waagsociety/air_quality_sensor_kit/Bora_Lora_Kit/eagle_files/lora_shield_top.png

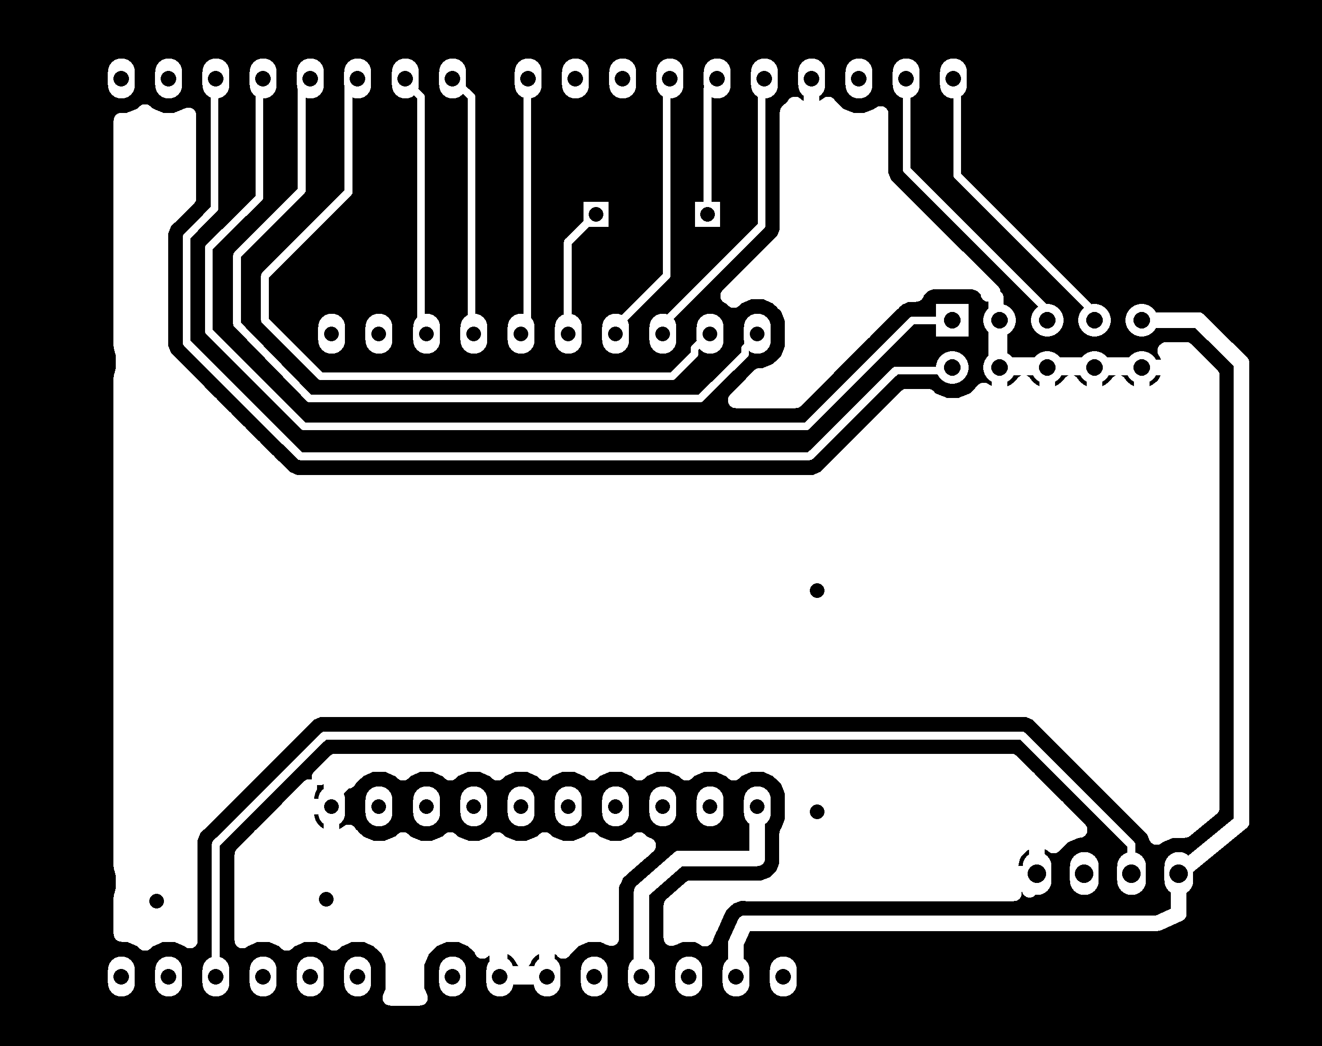
Bora_Lora_Kit/eagle_files/lora_shield_top.png
