waagsociety/air_quality_sensor_kit/MUV Kit/Case/Images/Process Photos/Process8.jpg

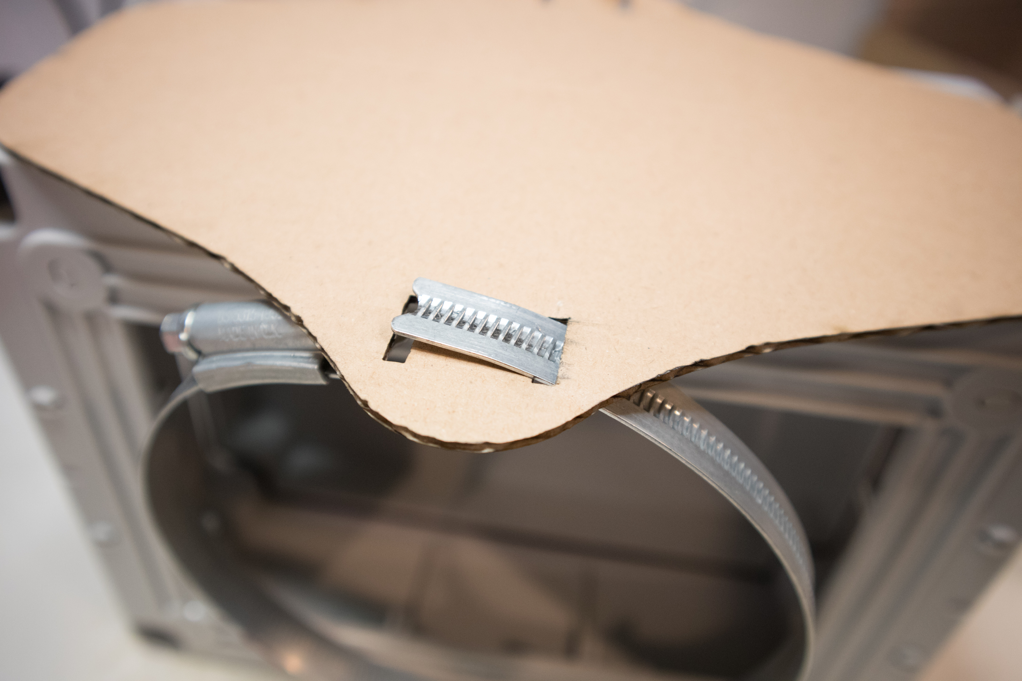
MUV Kit/Case/Images/Process Photos/Process8.jpg
