waagsociety/air_quality_sensor_kit/MUV Kit/Case/Images/Process Photos/Process21.jpg

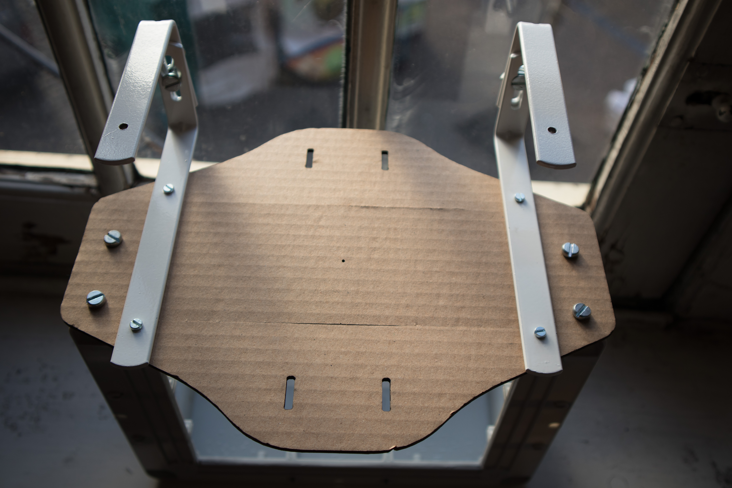
MUV Kit/Case/Images/Process Photos/Process21.jpg
