waagsociety/air_quality_sensor_kit/MUV Kit/Case/Images/Product Photos/Product2.jpg

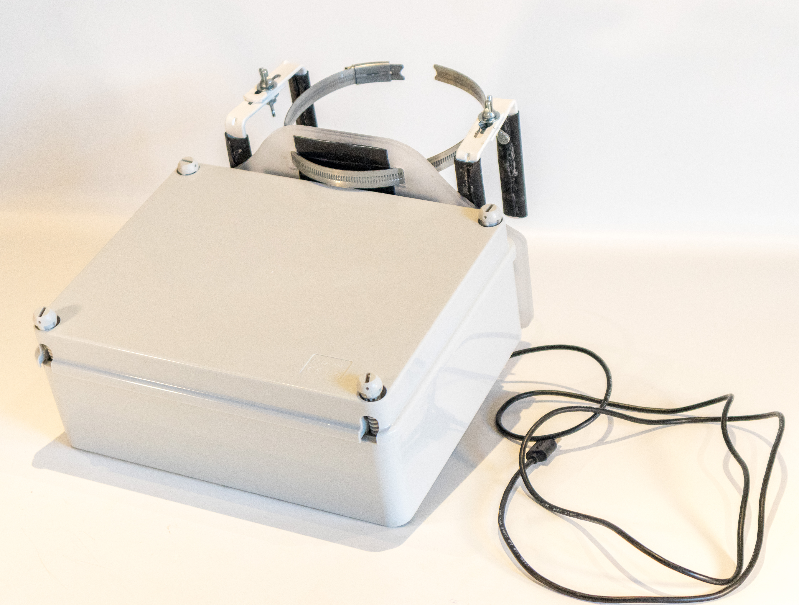
MUV Kit/Case/Images/Product Photos/Product2.jpg
