waagsociety/air_quality_sensor_kit/MUV Kit/Case/Images/Product Photos/Product4.jpg

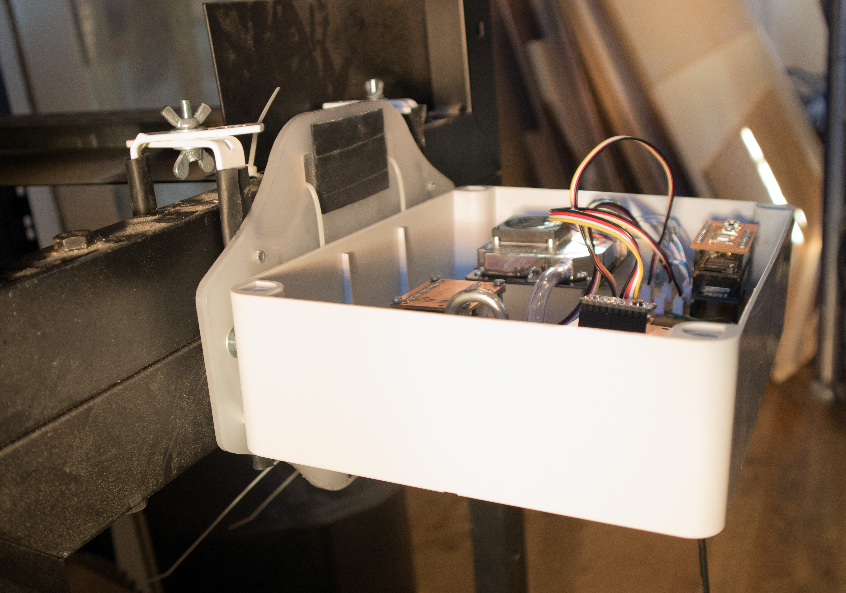
MUV Kit/Case/Images/Product Photos/Product4.jpg
