waagsociety/air_quality_sensor_kit/MUV Kit/Hardware/Machinable files/bme280_pcb_top_cut.png

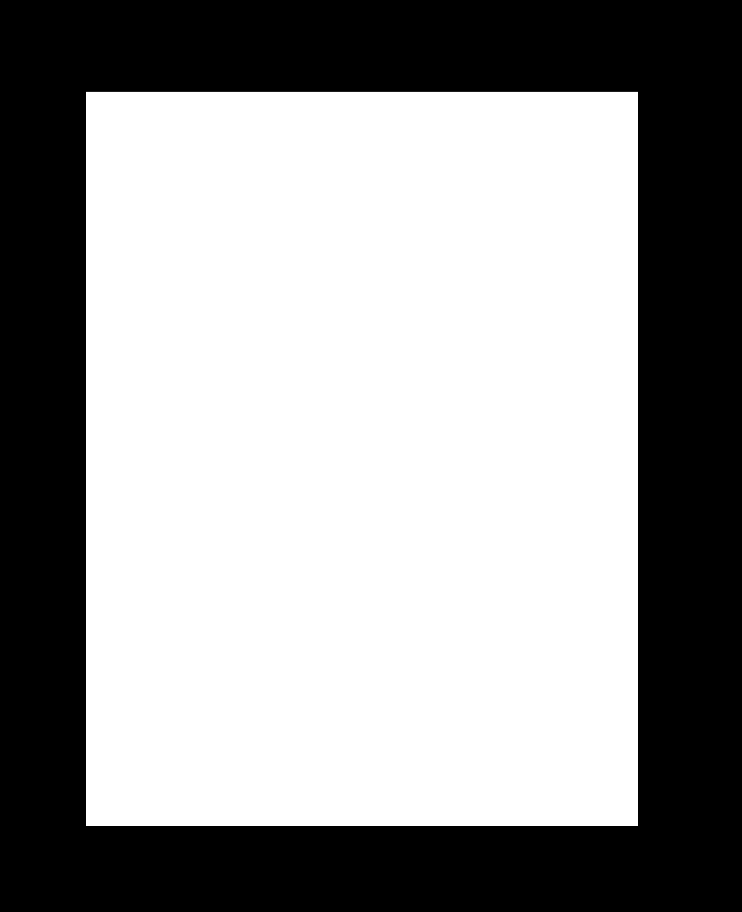
MUV Kit/Hardware/Machinable files/bme280_pcb_top_cut.png
