waagsociety/air_quality_sensor_kit/MUV Kit/Hardware/Machinable files/gas_pcb_bottom_cut.png

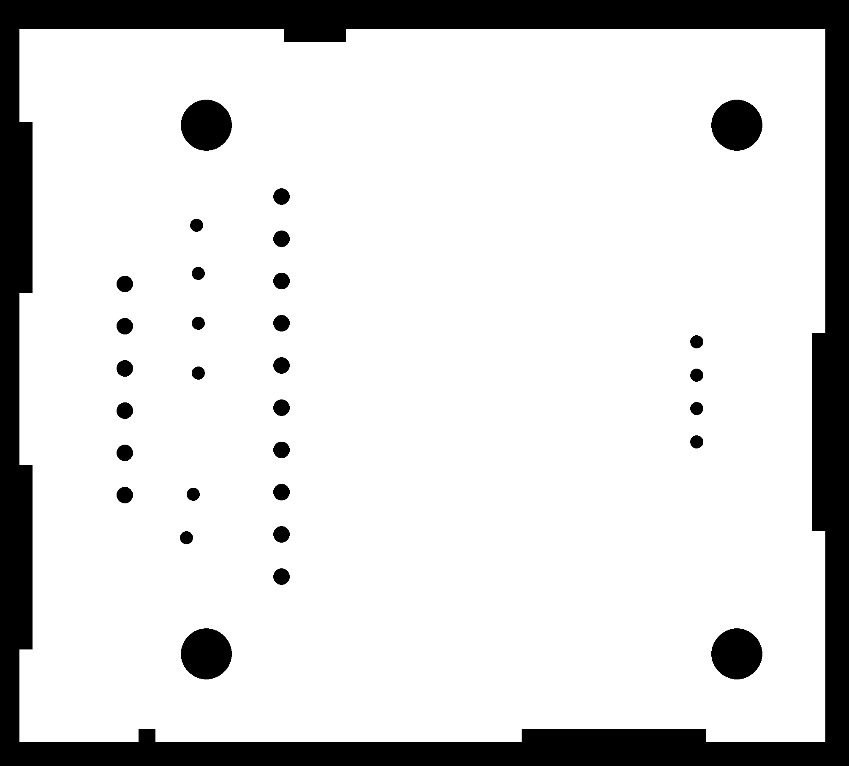
MUV Kit/Hardware/Machinable files/gas_pcb_bottom_cut.png
