waagsociety/air_quality_sensor_kit/MUV Kit/Hardware/Machinable files/interface_pcb_cut.png

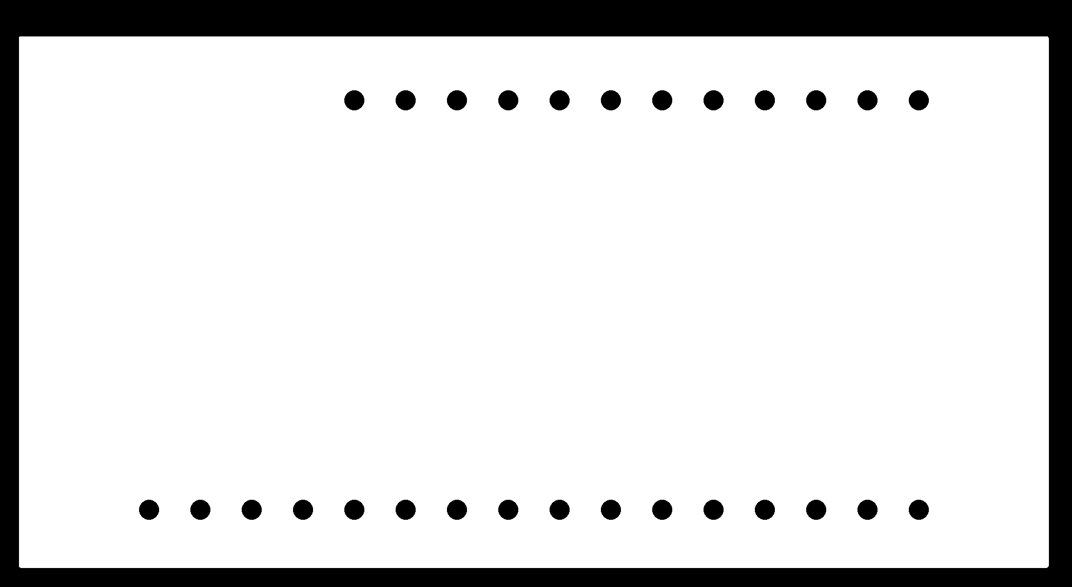
MUV Kit/Hardware/Machinable files/interface_pcb_cut.png
