waagsociety/air_quality_sensor_kit/MUV Kit/Hardware/Machinable files/interface_pcb_traces.png

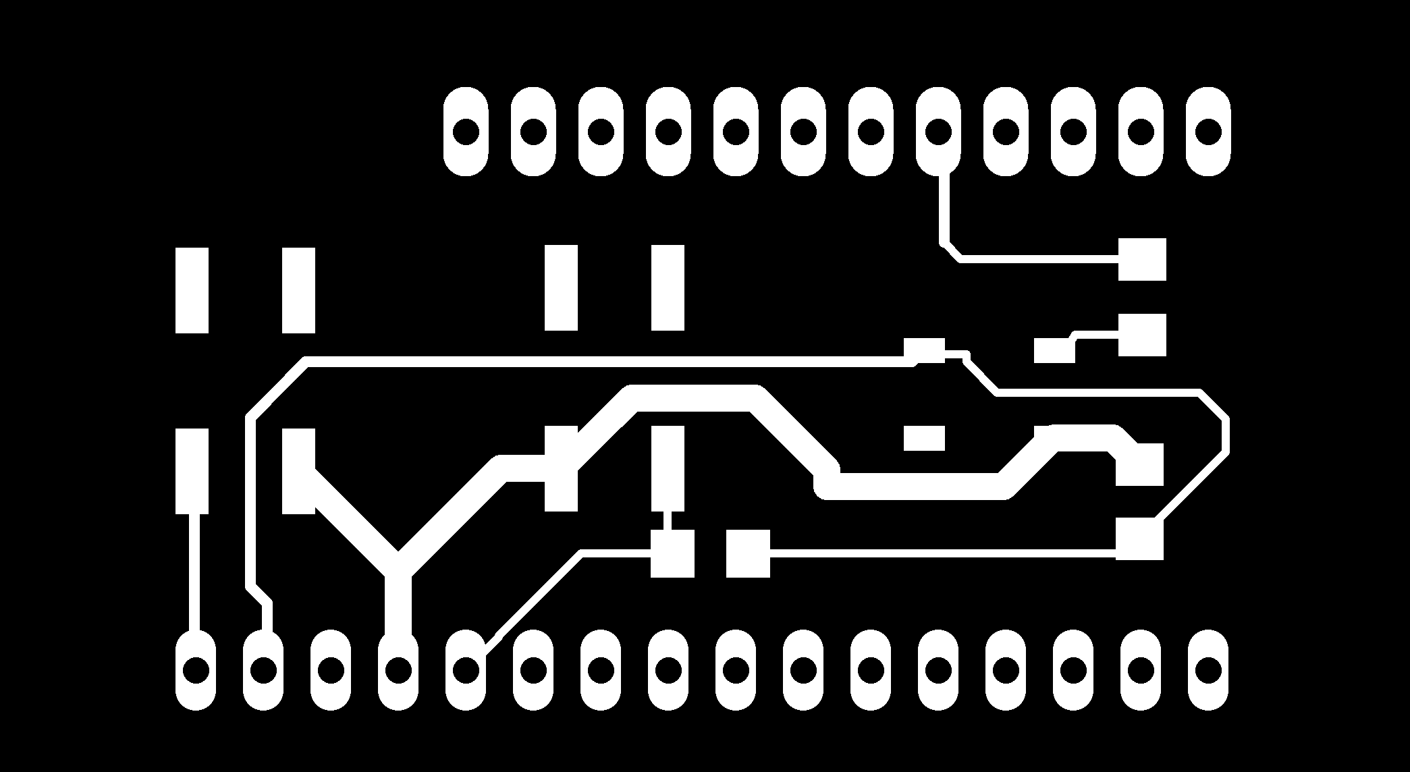
MUV Kit/Hardware/Machinable files/interface_pcb_traces.png
