waagsociety/air_quality_sensor_kit/MUV Kit/Hardware/Machinable files/muv_sensors_pcb_traces.png

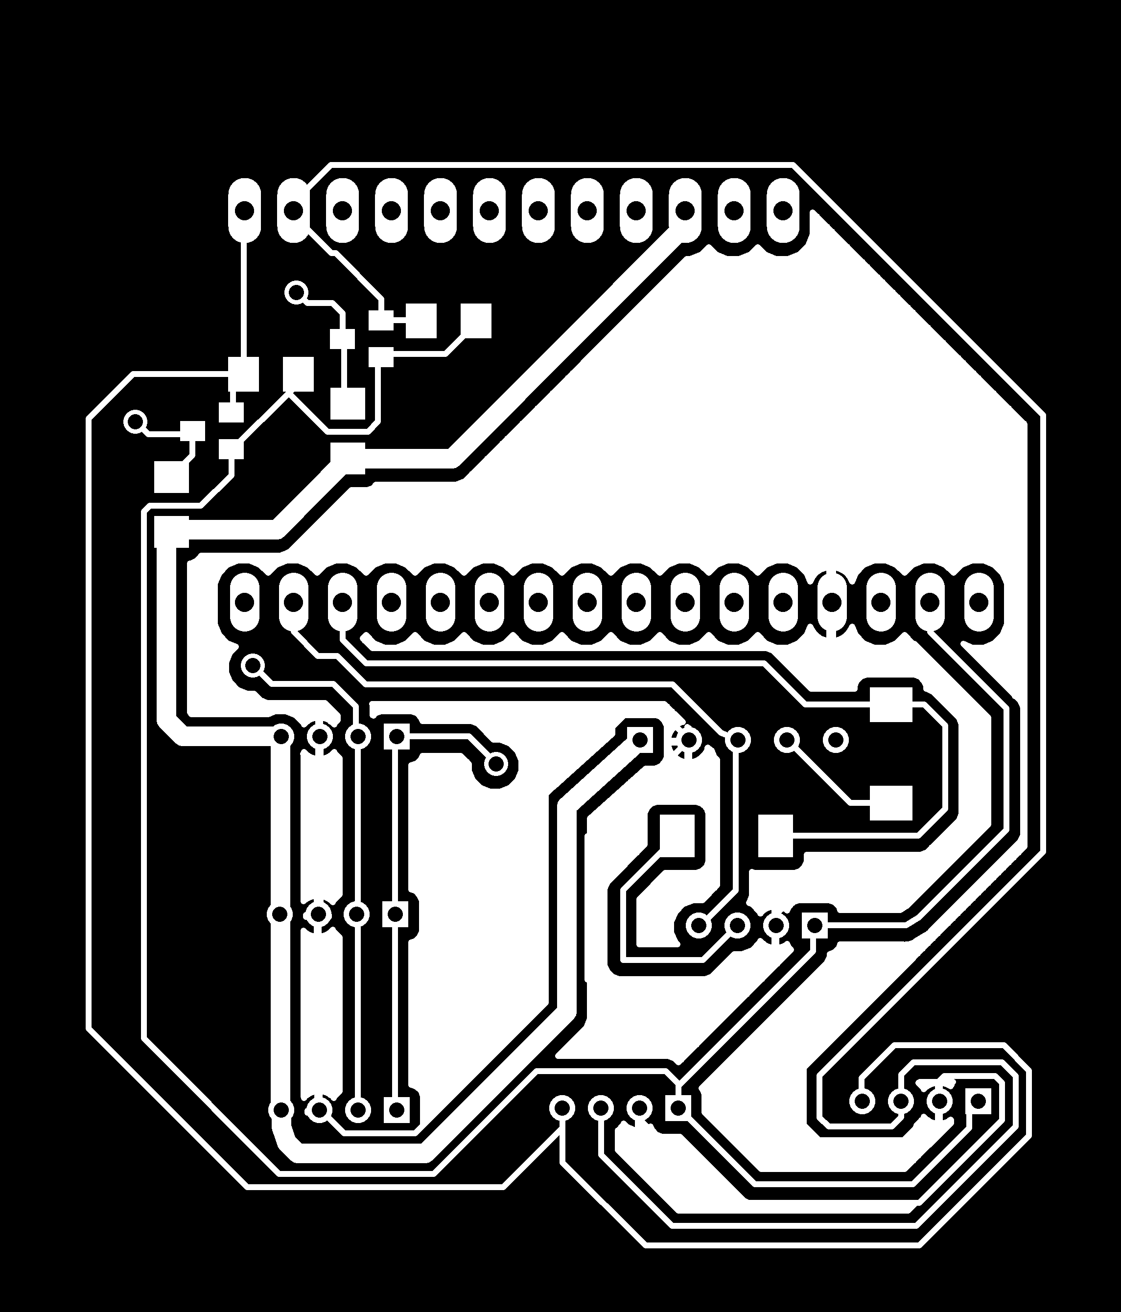
MUV Kit/Hardware/Machinable files/muv_sensors_pcb_traces.png
