waagsociety/air_quality_sensor_kit/Responsive_bird/casing/cutprints.png

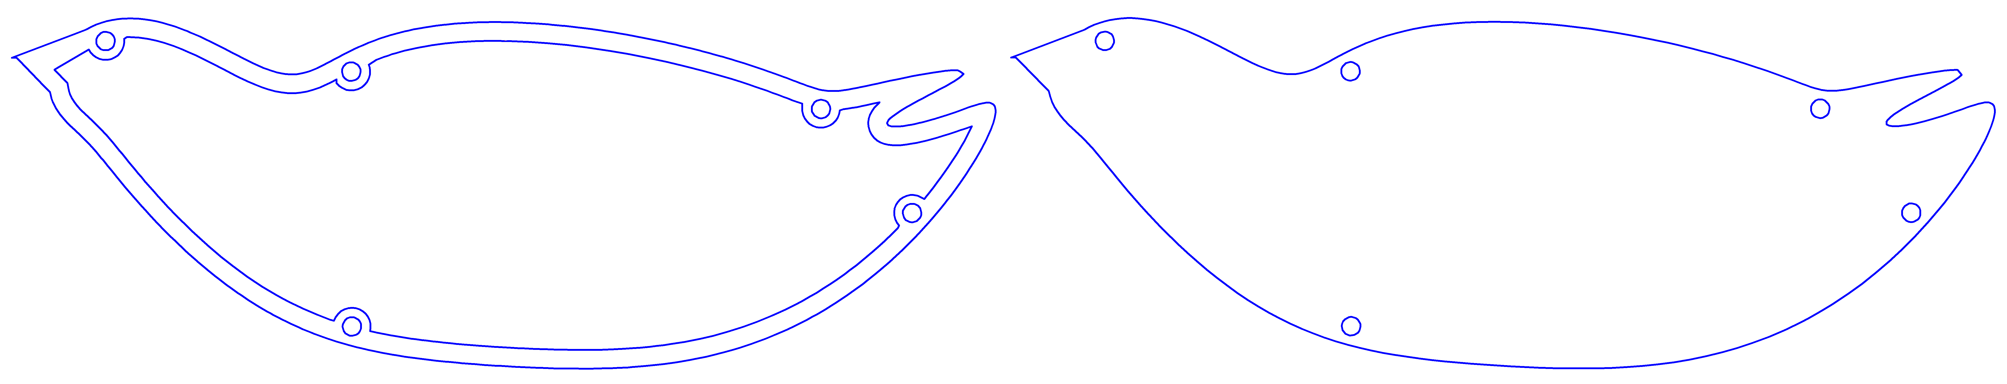
Responsive_bird/casing/cutprints.png
