waagsociety/air_quality_sensor_kit/Responsive_bird/pictures/IMG_2162.jpg

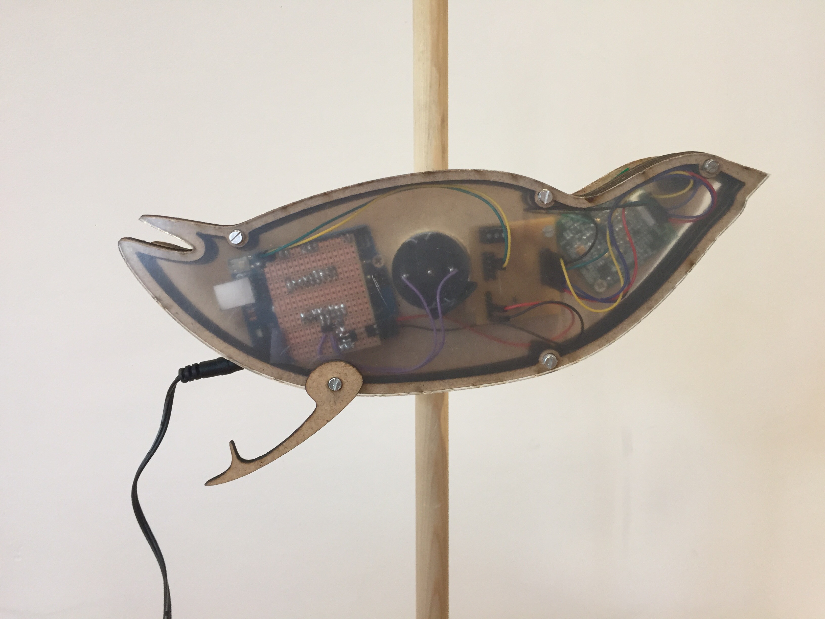
Responsive_bird/pictures/IMG_2162.jpg
